vam-polf/MPTT/firmware/startup.c

/* Minimal startup for STM32WLE5CBU6 */
#include <stdint.h>

extern uint32_t _estack;
extern uint32_t _sidata, _sdata, _edata, _sbss, _ebss;
extern int main(void);

void Reset_Handler(void) {
    /* Copy .data from flash to SRAM */
    uint32_t *src = &_sidata;
    uint32_t *dst = &_sdata;
    while (dst < &_edata) *dst++ = *src++;

    /* Zero .bss */
    dst = &_sbss;
    while (dst < &_ebss) *dst++ = 0;

    main();
    while(1);
}

void Default_Handler(void) { while(1); }

/* Vector table */
__attribute__((section(".isr_vector")))
const uint32_t vectors[] = {
    (uint32_t)&_estack,       /* Initial SP */
    (uint32_t)Reset_Handler,  /* Reset */
    (uint32_t)Default_Handler, /* NMI */
    (uint32_t)Default_Handler, /* HardFault */
    (uint32_t)Default_Handler, /* MemManage */
    (uint32_t)Default_Handler, /* BusFault */
    (uint32_t)Default_Handler, /* UsageFault */
    0, 0, 0, 0,              /* Reserved */
    (uint32_t)Default_Handler, /* SVCall */
    (uint32_t)Default_Handler, /* DebugMon */
    0,                        /* Reserved */
    (uint32_t)Default_Handler, /* PendSV */
    (uint32_t)Default_Handler, /* SysTick */
};
